wright-group/FilterWheels/chassis/small mount - threaded wheel/threaded filter wheel.pdf

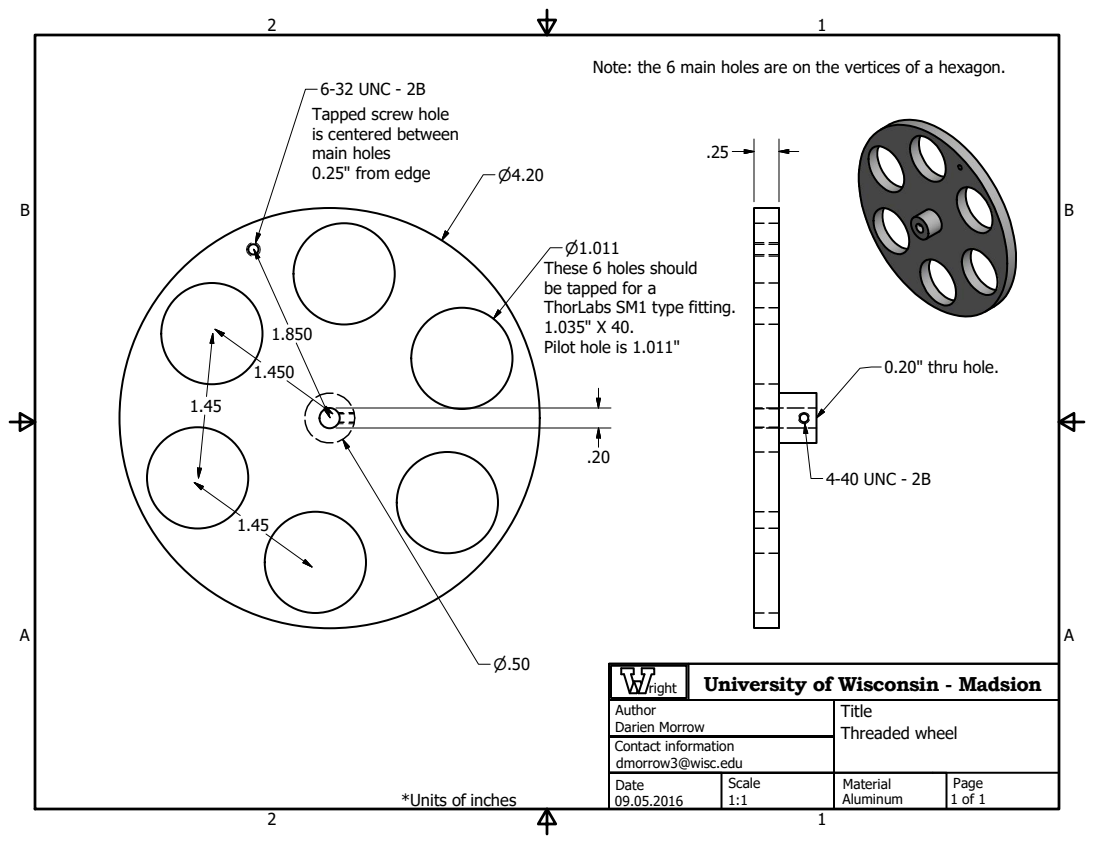
[picture p12: page 1]
Darien Morrow; dmorrow3@wisc.edu; Aluminum; Threaded wheel; Author; Date; Scale; Title; Material; Page; Contact information; right; 4-40 UNC - 2B; 0.20" thru hole.

Note: the 6 main holes are on the vertices of a hexagon.

6-32 UNC - 2B
Tapped screw hole
is centered between
main holes
0.25" from edge

These 6 holes should
be tapped for a
ThorLabs SM1 type fitting.
Pilot hole is 1.011"

University of Wisconsin - Madsion

*Units of inches
