wright-group/FilterWheels/controller/enclosure/back.pdf

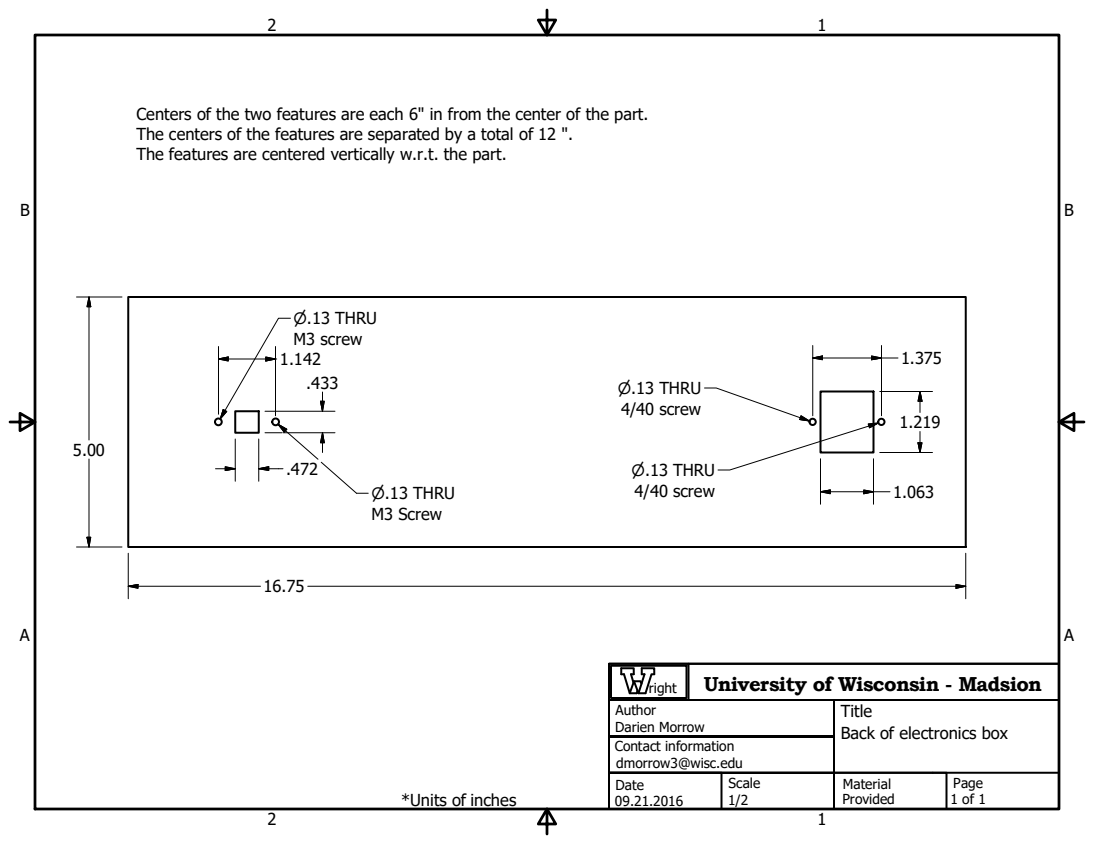
[picture p13: page 1]
Darien Morrow; dmorrow3@wisc.edu; Provided; Author; Date; Scale; Material; Page; Contact information; right; P.13 THRU; M3 screw; M3 Screw; 4/40 screw

Centers of the two features are each 6" in from the center of the part.
The centers of the features are separated by a total of 12 ".
The features are centered vertically w.r.t. the part.

University of Wisconsin - Madsion

Title
Back of electronics box

*Units of inches
