wright-group/FilterWheels/controller/enclosure/front.pdf

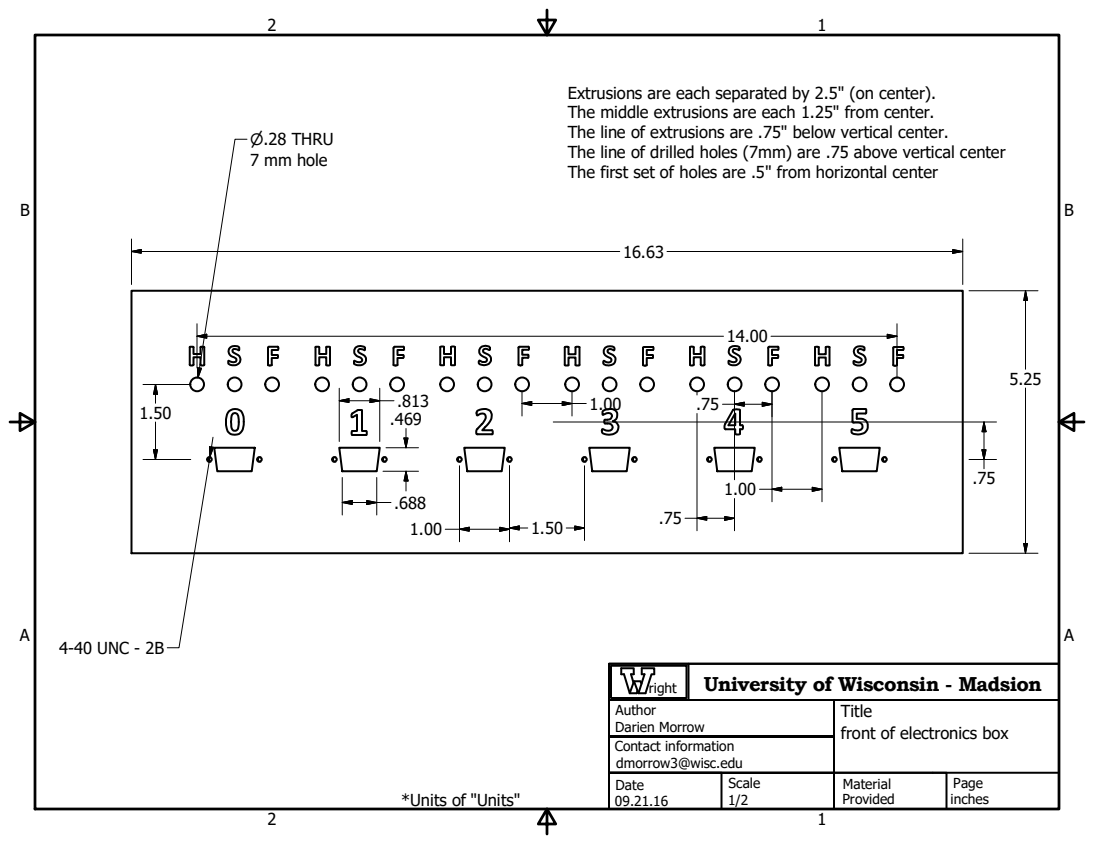
[picture p14: page 1]
Darien Morrow; dmorrow3@wisc.edu; Provided; inches; Author; Date; Scale; Material; Page; Contact information; right; P.28 THRU; 7 mm hole; 4-40 UNC - 2B

Extrusions are each separated by 2.5" (on center).
The middle extrusions are each 1.25" from center.
The line of extrusions are .75" below vertical center.
The line of drilled holes (7mm) are .75 above vertical center
The first set of holes are .5" from horizontal center

University of Wisconsin - Madsion

Title
front of electronics box

*Units of "Units"
