wright-group/FilterWheels/controller/enclosure/perforated side.pdf

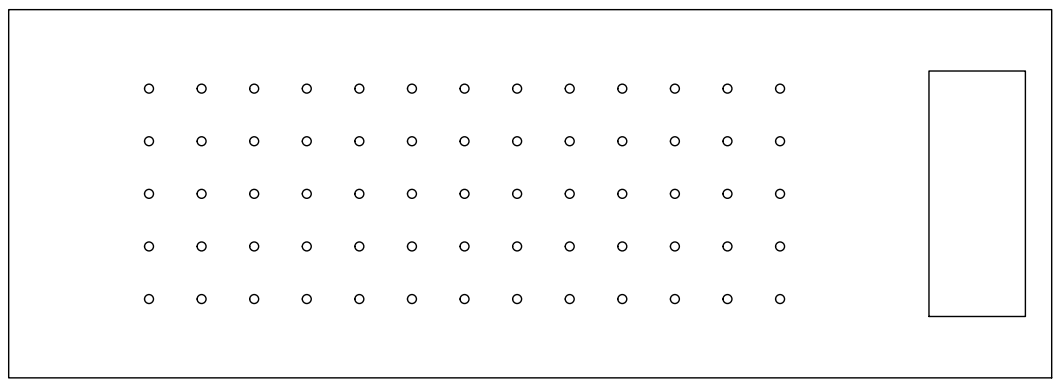
[picture p15: page 1]
SHEET 1 OF 1; DRAWN; CHECKED; MFG; APPROVED; Darien Morrow; DWG NO perforated side; TITLE; SIZE D; SCALE; REV
